JackOLntrn/EMBER/src/DRV8871Driver.h

/** @file DRV8871Driver.h
 * This file implements a class to provide basic control for 
 * a DRV8871 motor driver using PWM for speed control. 
 * To use this code you will need PWM capable output pins.
 * 
 * @brief DRV8871 motor driver class header
 * @author Jackson Cordova, GPT-5 mini
 * @date November 2025
 */

 #include <Arduino.h>


#ifndef DRV8871_DRIVER_H
#define DRV8871_DRIVER_H

/**
 * @class DRV8871Driver
 * @brief A class to add basic functions for DRV8871 Motor Driver
 *
 * 
 * @details This class enables drive, coast, and brake functions 
 * for a DRV8871 motor driver. It uses PWM for speed control and 
 * a digital pin for direction control. This class uses 8 bit
 * PWM resolution, so speed values should be integers from 0 to 255.
 * 
 * @tparam in1: PWM output pin (uses analogWrite)
 * @tparam in2: Direction pin (uses digitalWrite)
 */
class DRV8871Driver {
    protected:
        uint8_t in1Pin;      // PWM pin (attached to LEDC channel)
        uint8_t in2Pin;      // Direction pin (digital)
        
    public:
        /** @brief Constructor function which initializes the motor driver
         * 
         * @param in1 PWM output pin
         * @param in2 Direction pin
         */
        DRV8871Driver(uint8_t in1, uint8_t in2);

        /** @brief Function which drives the motor at a specified speed and direction
         * 
         * @param speed unsigned speed value. Range: 0 to max based on resolution
         * @param dir   Direction (true/false) written to the direction pin
         */
        void driveMotor(uint8_t speed, bool dir);

        /** @brief Coast motor to stop - lets the motor spin down by itself
         */
        void coastMotor(void);

        /** @brief Brake the motor Quickly - uses active braking to stop the motor
         */
        void brakeMotor(void);
};

#endif // DRV8871_DRIVER_H
