JackOLntrn/EMBER/src/task_motorControl.h

/** @file task_motorControl.h
 * 
 * @brief Motor control task header
 * @author Jackson Cordova, GPT5-mini
 * @date November 2025
 */

 #ifndef _task_motorControl_h
 #define _task_motorControl_h

void task_motorControl(void* p_params);

 #endif
