JackOLntrn/EMBER/src/task_stateMachine.h

/** @file task_stateMachine.h
 * 
 * @brief State machine task header
 * @author Jackson Cordova, GPT5-mini
 * @date December 2025
 */

 #ifndef _task_stateMachine_h
 #define _task_stateMachine_h

void task_stateMachine(void* p_params);

#endif
