JackOLntrn/EMBER/src/task_read_camera.cpp

/** @file task_read_camera.cpp
 * 
 * @brief Thermal camera reading and hot blob detection task
 * @author Jackson Cordova, GPT5-mini
 * @date November 2025
 */

#include "PrintStream.h"
#include "task_read_camera.h"
#include <Arduino.h>
#include <Wire.h>
#include "shares.h"
#include "task_webserver.h"
#include "adafruit_mlx90640.h"

// Temperature thresholds for hotblob detection and fire alerts (°C)
#define HOTBLOB_DETECT_THRESHOLD 50.0f     // Trigger blob detection when hottest pixel exceeds this
#define HOTBLOB_INCLUSION_THRESHOLD 49.0f  // Include neighboring pixels >= this temp in blob
#define FIRE_ALERT_THRESHOLD 70.0f         // Trigger fire alert when blob max temp exceeds this
#define FIRE_COOLDOWN_THRESHOLD 60.0f      // Turn off fire alert when temp drops below this

#define NUM_PIXELS 768


Adafruit_MLX90640 mlx;


/** @brief function which finds the centroid of a hot blob in a thermal frame
 * 
 * @details this functions performs a breadth-first search (BFS) starting from a seed pixel
 * to find all connected pixels above a temperature threshold, effectively identifying a 
 * "blob" of hot pixels. It computes the weighted centroid of the blob based on pixel temperatures,
 * as well as the maximum temperature, average temperature, and size of the blob.
 * 
 * @param frame pointer to the thermal frame array (size 768)
 * @param seedIdx index of the seed pixel to start the search from
 * @param tempThreshold temperature threshold for including pixels in the blob
 * @param outCentroidIdx reference to store the index of the computed centroid pixel
 * @param outMaxTemp reference to store the maximum temperature found in the blob
 * @param outAvgTemp reference to store the average temperature of the blob
 * @param outSize reference to store the size (number of pixels) of the blob
 * @param outCentroidX reference to store the X coordinate of the centroid
 * @param outCentroidY reference to store the Y coordinate of the centroid
 */
void findHotBlob(const float* frame, uint16_t seedIdx, float tempThreshold, 
                 uint16_t& outCentroidIdx, float& outMaxTemp, float& outAvgTemp,
                 uint16_t& outSize, float& outCentroidX, float& outCentroidY)
{
    // 32x24 grid
    const uint16_t W = 32;
    const uint16_t H = 24;
    
    static bool visited[NUM_PIXELS] = {false};
    memset(visited, 0, sizeof(visited));
    
    // BFS to find connected blob
    uint16_t queue[NUM_PIXELS];
    uint16_t qhead = 0, qtail = 0;
    
    queue[qtail++] = seedIdx;
    visited[seedIdx] = true;
    
    float sumTemp = 0;
    float sumWeightedX = 0;
    float sumWeightedY = 0;
    float totalWeight = 0;
    outMaxTemp = frame[seedIdx];
    
    while (qhead < qtail && qtail < NUM_PIXELS) {
        uint16_t idx = queue[qhead++];
        uint16_t x = idx % W;
        uint16_t y = idx / W;
        
        float temp = frame[idx];
        float weight = temp - (tempThreshold - 5);  // weight by how hot it is
        weight = max(0.0f, weight);
        
        sumTemp += temp;
        sumWeightedX += x * weight;
        sumWeightedY += y * weight;
        totalWeight += weight;
        outMaxTemp = max(outMaxTemp, temp);
        
        // Check 4-neighbors (up, down, left, right)
        // Up
        if (y > 0) {
            uint16_t nidx = (y - 1) * W + x;
            if (!visited[nidx] && frame[nidx] >= tempThreshold) {
                visited[nidx] = true;
                queue[qtail++] = nidx;
            }
        }
        // Down
        if (y < H - 1) {
            uint16_t nidx = (y + 1) * W + x;
            if (!visited[nidx] && frame[nidx] >= tempThreshold) {
                visited[nidx] = true;
                queue[qtail++] = nidx;
            }
        }
        // Left
        if (x > 0) {
            uint16_t nidx = y * W + (x - 1);
            if (!visited[nidx] && frame[nidx] >= tempThreshold) {
                visited[nidx] = true;
                queue[qtail++] = nidx;
            }
        }
        // Right
        if (x < W - 1) {
            uint16_t nidx = y * W + (x + 1);
            if (!visited[nidx] && frame[nidx] >= tempThreshold) {
                visited[nidx] = true;
                queue[qtail++] = nidx;
            }
        }
    }
    
    // Compute weighted centroid
    outSize = qtail;
    if (totalWeight > 0) {
        float centX = sumWeightedX / totalWeight;
        float centY = sumWeightedY / totalWeight;
        outCentroidX = centX;
        outCentroidY = centY;
        // Find nearest actual pixel to centroid
        float minDist = 1e9f;
        outCentroidIdx = seedIdx;
        for (uint16_t idx = 0; idx < NUM_PIXELS; idx++) {
            if (visited[idx]) {
                uint16_t x = idx % W;
                uint16_t y = idx / W;
                float dx = x - centX;
                float dy = y - centY;
                float dist = dx * dx + dy * dy;
                if (dist < minDist) {
                    minDist = dist;
                    outCentroidIdx = idx;
                }
            }
        }
        outAvgTemp = sumTemp / (float)outSize;  // average of all pixels in blob
    } else {
        outCentroidIdx = seedIdx;
        outAvgTemp = frame[seedIdx];
        outCentroidX = seedIdx % W;
        outCentroidY = seedIdx / W;
    }
}


/** @brief task which reads the MLX90640 thermal camera and detects hotspots
 * 
 * @details This task continuously reads frames from the MLX90640 thermal camera at a 
 * set refresh rate. It processes each frame to find the hottest pixel and then identifies 
 * a connected "hot blob" of pixels around it that exceed a defined temperature threshold.
 * The task computes the centroid of the hot blob and applies temporal smoothing to reduce 
 * jitter in the detected position. If the maximum temperature of the blob exceeds a fire 
 * alert threshold, it sets a shared boolean "fire" to true. The task runs indefinitely with 
 * no delay, relying on the camera's refresh rate for timing.  
 * 
 * @param p_params not used and should be set to void in the xTaskCreate call     
 */
void task_read_camera(void* p_params) {
    long n = 0;
    fire.put(false);
    Wire.begin(21,22);
    Wire.setClock(400000); // 400kHz I2C
    float highestTemp = 0;
    uint16_t maxIndex = 0;
    uint8_t nframes = 0;
    
    if (!mlx.begin(MLX90640_I2CADDR_DEFAULT, &Wire)) {
        while(1) { Serial.println("MLX90640 not found"); delay(1000); }
    }
    mlx.setMode(MLX90640_CHESS);
    mlx.setResolution(MLX90640_ADC_18BIT);
    mlx.setRefreshRate(MLX90640_16_HZ); // try 8–16 Hz

    while(true) {
        if(!mlx.getFrame(Frame)) {
            //n++;
            //Serial << (millis()/1000) << " : " << n << endl;

            // Find the single hottest pixel first
            highestTemp = Frame[0];
            maxIndex = 0;
            for (uint16_t i = 1; i < NUM_PIXELS; i++) {
                if (Frame[i] > highestTemp) {
                    highestTemp = Frame[i];
                    maxIndex = i;
                }
            }

            // If hottest pixel is above threshold, find the hot blob around it
            if (highestTemp > HOTBLOB_DETECT_THRESHOLD) {
                uint16_t blobCentroid = maxIndex;
                float blobMaxTemp = highestTemp;
                float blobAvgTemp = highestTemp;
                uint16_t blobSize = 0;
                float blobCentX = 0.0f, blobCentY = 0.0f;

                // Find connected blob of pixels >= HOTBLOB_INCLUSION_THRESHOLD around the hotspot
                findHotBlob(Frame, maxIndex, HOTBLOB_INCLUSION_THRESHOLD, blobCentroid, blobMaxTemp, blobAvgTemp, blobSize, blobCentX, blobCentY);

                // Temporal smoothing (exponential moving average) on centroid to reduce jitter
                const float alpha = 0.25f; // smoothing factor (0..1), smaller = smoother
                static float smoothX = 0.0f, smoothY = 0.0f;
                static bool smoothInit = false;
                if (!smoothInit) {
                    smoothX = blobCentX;
                    smoothY = blobCentY;
                    smoothInit = true;
                } else {
                    smoothX = alpha * blobCentX + (1.0f - alpha) * smoothX;
                    smoothY = alpha * blobCentY + (1.0f - alpha) * smoothY;
                }

                // Round smoothed position to nearest pixel index
                uint16_t smoothXi = (uint16_t)constrain((int)roundf(smoothX), 0, 31);
                uint16_t smoothYi = (uint16_t)constrain((int)roundf(smoothY), 0, 23);
                uint16_t smoothIdx = smoothYi * 32 + smoothXi;

                // Only update hotIndex if blob is reasonably large or sufficiently hot
                if (blobSize >= 2 || blobMaxTemp > 48.0f) {
                    hotIndex.put(smoothIdx);
                } else {
                    // small blob - do not update to avoid noise
                }

                if (blobMaxTemp > FIRE_ALERT_THRESHOLD) {
                    fire.put(true);
                }
            } else {
                // No significant blob: fallback to single-pixel smoothing
                static float smoothX = 0.0f, smoothY = 0.0f;
                static bool smoothInit = false;
                float px = maxIndex % 32;
                float py = maxIndex / 32;
                const float alpha = 0.25f;
                if (!smoothInit) {
                    smoothX = px; smoothY = py; smoothInit = true;
                } else {
                    smoothX = alpha * px + (1.0f - alpha) * smoothX;
                    smoothY = alpha * py + (1.0f - alpha) * smoothY;
                }
                uint16_t smoothXi = (uint16_t)constrain((int)roundf(smoothX), 0, 31);
                uint16_t smoothYi = (uint16_t)constrain((int)roundf(smoothY), 0, 23);
                uint16_t smoothIdx = smoothYi * 32 + smoothXi;
                hotIndex.put(smoothIdx);

                if (highestTemp > 70) {
                    fire.put(true);
                }
            }
            
            if (highestTemp < FIRE_COOLDOWN_THRESHOLD && fire.get() && nframes > 5 ) {
                fire.put(false);
                nframes = 0;
            }
            else if (highestTemp < HOTBLOB_DETECT_THRESHOLD && fire.get()) {
                nframes++;
            }
        }
    }
}
