JackOLntrn/EMBER/src/task_read_camera.h

/** @file task_read_camera.h
 * 
 * @brief Thermal camera task header
 * @author Jackson Cordova, GPT5-mini
 * @date November 2025
 */


 #ifndef _task_read_camera_h
 #define _task_read_camera_h

 void task_read_camera(void* p_params);
 
 #endif
