JackOLntrn/EMBER/src/task_webserver.h

/** @file task_webserver.h
 * 
 * @brief Web server task header
 * @author Jackson Cordova
 * @date December 2025
 */

 #ifndef _task_webserver_h_
 #define _task_webserver_h_
 #undef USE_LAN


 void task_webserver (void* p_params);
 void setup_wifi(void);
 
 #endif
